tungusk/strampler-build-pack/bom/BOM-ctag-RevD-reference.xlsx

Designator | Package | Quantity | Designation | Mouser | Remarks
LCD501 | TFT_2.2 | 1 | TFT_ILI9341 | MDF7-9S-2.54DSA(55) |  | https://www.aliexpress.com/item/Smart-Electronics-2-2-Inch-240-320-Dots-SPI-TFT-LCD-Serial-Port-Module-Display-ILI9341/32607741715.html
C505,C504,C503,C813,C302,C402,C601,C605,C706,C712,C715,C716,C720,C721,C801,C804,C807,C810,C713 | C_0603_1608Metric | 19 | 100n | 81-GRM033C71C104KE4J (https://www.mouser.de/ProductDetail/Murata-Electronics/GRM033C71C104KE14J)
U301 | QFN-24-1EP_4x4mm_P0.5mm_EP2.6x2.6mm | 1 | CP2102N-A01-GQFN24 | 634-CP2102NA01GQFN24
D604 | LED_D5.0mm_Clear | 1 | ~ | 743-INL-5AR30 (https://www.mouser.de/QuickViewProdDetail.aspx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) |  | Larger angle and intensity: | 941-C5SMFRJECT0W0BB2
U202 | SOT-23 | 1 | MIC803 | 998-MIC803-31D3VM3TR
U601 | SIP3_11.6x8.5mm | 1 | R-78E3.3-1.0 | 919-R-78E3.3-1.0
R603 | R_2512_6332Metric | 1 | 10 | 279-CRGP2512F10R
C608 | CP_Elec_10x12.6 | 1 | 1000u | 661-APXG160A102MJA0G
C815,C202,C814 | C_0603_1608Metric | 3 | 1u | 603-CC603KRX7R7BB105 | X7R
U201 | ESP32-WROVER | 1 | ESP32-WROVER | 356-ESP32WROIB(16MB) |  | Important use WROVER-B the non-B has boot issues |  |  | For IPEX use e.g. this antenna | https://de.aliexpress.com/item/1pcs-2-4Ghz-Antenna-SMA-male-3dbi-Zigbee-wifi-antenna-mini-short-rubber-aerial-SMA/32813612333.html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
C201,C401,C501,C607,C701,C705,C707,C710,C714,C718,C719,C722,C502,C301,C711 | C_0805_2012Metric | 15 | 10u | 81-GRM21BR70J106KA3L (https://www.mouser.de/ProductDetail/Murata-Electronics/GRM21BR70J106KA73L) | X7R
C602,C603,C604 | CP_EIA-3216-12_Kemet-S | 3 | 22u | 647-F931C226MAA (https://www.mouser.de/ProductDetail/AVX/F951C226KQAAQ2)
C702,C708 | C_0603_1608Metric | 2 | 220p | 710-885012206055 (https://www.mouser.de/ProductDetail/Wurth-Electronics/885012206055)
C703,C704,C709,C717 | C_0603_1608Metric | 4 | 18p | 80-C0603C180J5G
C802,C803,C805,C806,C808,C809,C811,C812 | C_0603_1608Metric | 8 | 1n | 77-VJ0603Y102KXQCBC (https://www.mouser.de/ProductDetail/Vishay-Vitramon/VJ0603Y102KXQCW1BC)
D601,D603 | D_SOD-123 | 2 | STPS2L40ZFY | 511-STPS2L40ZFY
D602 | SOT-23 | 1 | LM4040B-10 | 595-LM4040B10IDBZR (https://www.mouser.de/ProductDetail/Texas-Instruments/LM4040B10IDBZR)
J302 | USB_Micro-B_Molex-105017-0001 | 1 | USB_B_Micro | 105017-0001 (https://www.mouser.de/ProductDetail/Molex/105017-0001)
J402 | microSD_HC_Hirose_DM3D-SF | 1 | Micro_SD_Card | 798-DM3D-SF (https://www.mouser.de/ProductDetail/Hirose-Connector/DM3D-SF)
J601 | PinHeader_2x05_P2.54mm_Vertical | 1 | PWR |  | Standard 2,54mm
J702 | THONKICONN | 1 | RIN |  | PJ398SM | https://www.thonk.co.uk/shop/thonkiconn/
J703 | THONKICONN | 1 | LIN/MONO |  | PJ398SM | https://www.thonk.co.uk/shop/thonkiconn/
J704 | THONKICONN | 1 | ROUT |  | PJ398SM | https://www.thonk.co.uk/shop/thonkiconn/
J705 | THONKICONN | 1 | LOUT |  | PJ398SM | https://www.thonk.co.uk/shop/thonkiconn/
J801 | THONKICONN | 1 | TRG0 |  | PJ398SM | https://www.thonk.co.uk/shop/thonkiconn/
J802 | THONKICONN | 1 | CVIN1 |  | PJ398SM | https://www.thonk.co.uk/shop/thonkiconn/
J803 | THONKICONN | 1 | CVIN3 |  | PJ398SM | https://www.thonk.co.uk/shop/thonkiconn/
J804 | THONKICONN | 1 | CVIN2 |  | PJ398SM | https://www.thonk.co.uk/shop/thonkiconn/
J805,J807 | THONKICONN | 2 | CVIN4 |  | PJ398SM | https://www.thonk.co.uk/shop/thonkiconn/
J806 | THONKICONN | 1 | TRG1 |  | PJ398SM | https://www.thonk.co.uk/shop/thonkiconn/
J808 | THONKICONN | 1 | CVIN5 |  | PJ398SM | https://www.thonk.co.uk/shop/thonkiconn/
J809 | THONKICONN | 1 | CVIN6 |  | PJ398SM | https://www.thonk.co.uk/shop/thonkiconn/
J810 | THONKICONN | 1 | CVIN7 |  | PJ398SM | https://www.thonk.co.uk/shop/thonkiconn/
L601,L602 | C_0805_2012Metric | 2 | 600 | 623-2508056017Y2
Q301,Q302,Q303,Q801,Q802 | SOT-23 | 5 | SS8050-G | 750-SS8050-G
RV701 | Alpha_9mm_stereo | 1 | 50k audio |  | VERTICAL - DUAL GANG/STEREO: A50K - 50K Audio | https://www.thonk.co.uk/shop/alpha-9mm-pots/
RV801,RV802,RV803,RV804 | Alpha_9mm | 4 | 10k lin |  | VERTICAL: B10K - 10K Linear | https://www.thonk.co.uk/shop/thonkiconn/
SW501 | RotaryEncoder_Alps_EC11E-Switch_Vertical_H20mm | 1 | SEL |  |  | https://www.aliexpress.com/item/10pcs-Rotary-encoder-code-switch-EC11-audio-digital-potentiometer-with-switch-5Pin-handle-length-20mm-WAVGAT/32839106848.html
SW801 | SW_6425 | 1 | TRG0 | 979-6425.0101 | Cap | 979-826.000.071 | Or black | 826000011
SW802 | SW_6425 | 1 | TRG1 | 979-6425.0101 | Cap | 979-826.000.071 |  | 826000011
U602 | TSOT-23-5 | 1 | ADP7118 | 584-ADP7118AUJZ3.3R7
U701 | SSOP-28_5.3x10.2mm_P0.65mm | 1 | WM8731 | 238-WM8731SEDS/V (https://www.mouser.de/ProductDetail/Cirrus-Logic/WM8731SEDS-V?qs=sGAEpiMZZMthNezIpKscMWquczdXLZMI)
U702 | TSSOP-14_4.4x5mm_P0.65mm | 1 | TL074 | 595-TL074CPWR (https://www.mouser.de/ProductDetail/Texas-Instruments/TL074CPWR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)
U801,U802 | TSSOP-14_4.4x5mm_P0.65mm | 2 | MCP6004 | 579-MCP6004-I/ST (https://www.mouser.de/ProductDetail/Microchip-Technology/MCP6004-I-ST)
U803 | SOIC-16_3.9x9.9mm_P1.27mm | 1 | MCP3208 | 579-MCP3208T-CI/SL (https://www.mouser.de/ProductDetail/Microchip-Technology/MCP3208T-CI-SL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)
Y701 | Crystal_SMD_HC49-SD | 1 | 11.289600MHz | 815-ABLS211.2896B4YT (https://www.mouser.de/ProductDetail/ABRACON/ABLS2-112896MHz-B4Y-T)
R201,R301,R305,R306,R401,R402,R403,R404,R501,R502,R503,R802,R817,R302 | R_0603_1608Metric | 14 | 10k | 652-CR0603FX-1002ELF | 1%
R303 | R_0603_1608Metric | 1 | 22.1k | 652-CR0603FX-2212ELF (https://www.mouser.de/ProductDetail/Bourns/CR0603-FX-2212ELF) | 1%
R304 | R_0603_1608Metric | 1 | 47.5k | 603-RC0603FR-0747K5L (https://www.mouser.de/ProductDetail/Yageo/RC0603FR-0747K5L) | 1%
R601 | R_0603_1608Metric | 1 | 220 | 652-CR0603FX-2200ELF | 1%
R602 | R_0805_2012Metric | 1 | 68 | 603-AC0603FR-0768RL | 1%
R701,R705 | R_0603_1608Metric | 2 | 3k3 | 652-CR0603-FX3301ELF | 1%
R702,R706 | R_0603_1608Metric | 2 | 22k | 652-CR0603FX-2202ELF | 1%
R703,R704,R707,R708,R710,R714 | R_0603_1608Metric | 6 | 5k6 | 652-CR0603FX-5601ELF | 1%
R709,R712,R713,R716 | R_0603_1608Metric | 4 | 39k | 652-CR0603FX-3902ELF | 1%
R711,R715 | R_0603_1608Metric | 2 | 1k | 652-CR0603FX-1001ELF | 1%
R803,R810 | R_0603_1608Metric | 2 | 180k | 652-CR0603FX-1803ELF | 1%
R804,R811 | R_0603_1608Metric | 2 | 47k | 652-CR0603FX-4702ELF (https://www.mouser.de/ProductDetail/Bourns/CR0603-FX-4702ELF) | 1%
R805,R812,R819,R821,R825,R827 | R_0603_1608Metric | 6 | 200k | 652-CR0603FX-2003ELF | 1%
R806,R813 | R_0603_1608Metric | 2 | 33k | 652-CR0603FX-3302ELF | 1%
R807,R808,R809,R815,R816,R818,R823,R824,R829,R830 | R_0603_1608Metric | 10 | 100k | 603-RC0603FR-07100KL (https://www.mouser.de/ProductDetail/Yageo/RC0603FR-07100KL) | 1%
R820,R822,R826,R828 | R_0603_1608Metric | 4 | 66.5k | 652-CR0603-FX6652ELF | 1%
J701 | PinHeader_2x05_P2.54mm_Vertical_SMD | 1 | AUEXT |  | Standard 2,54mm SMD
C606 | C_1210_3225Metric | 1 | 10u | 710-885012209005 | X7R 16V
TP101 | TestPoint_Keystone_5019_Minature | 1 | TP_IO19 | 534-5019
